yesitsfebreeze/feb42/pcb/feb42.kicad_sch

## KiCad design pcb/feb42.kicad_sch (2024-09-22)

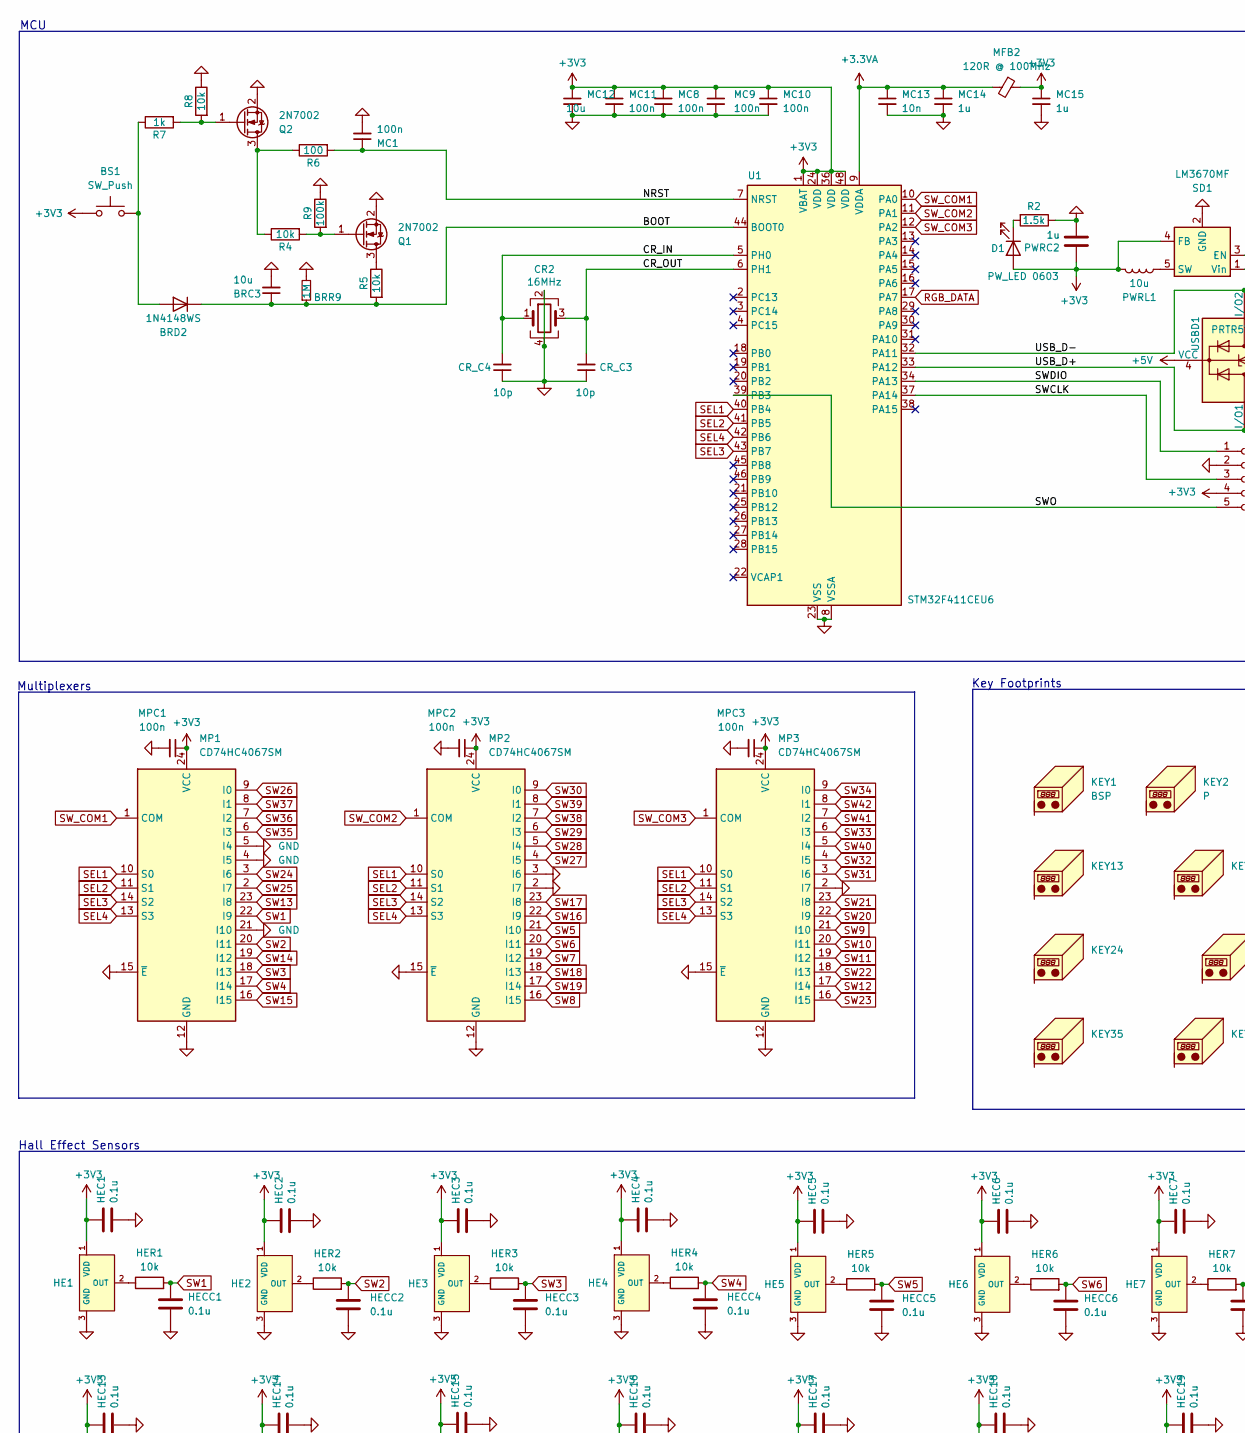
[picture p4: schematic feb42.kicad_sch, part in row 1, column 1]

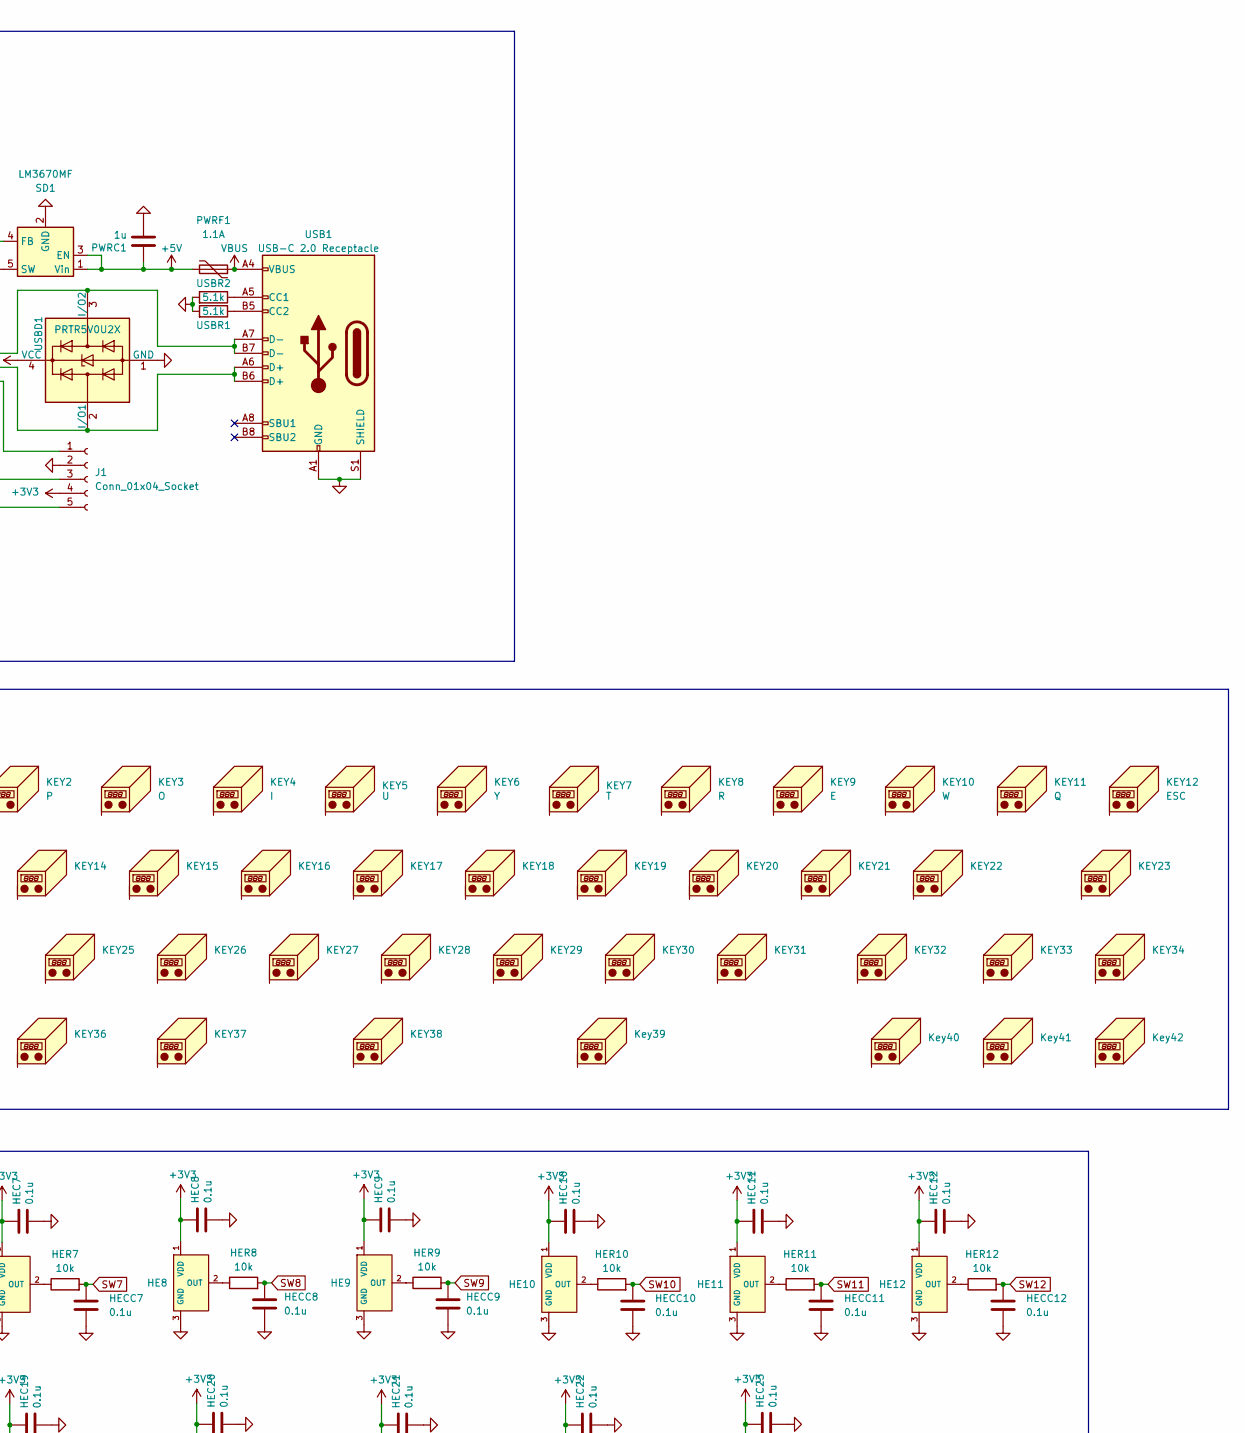
[picture p5: schematic feb42.kicad_sch, part in row 1, column 2]

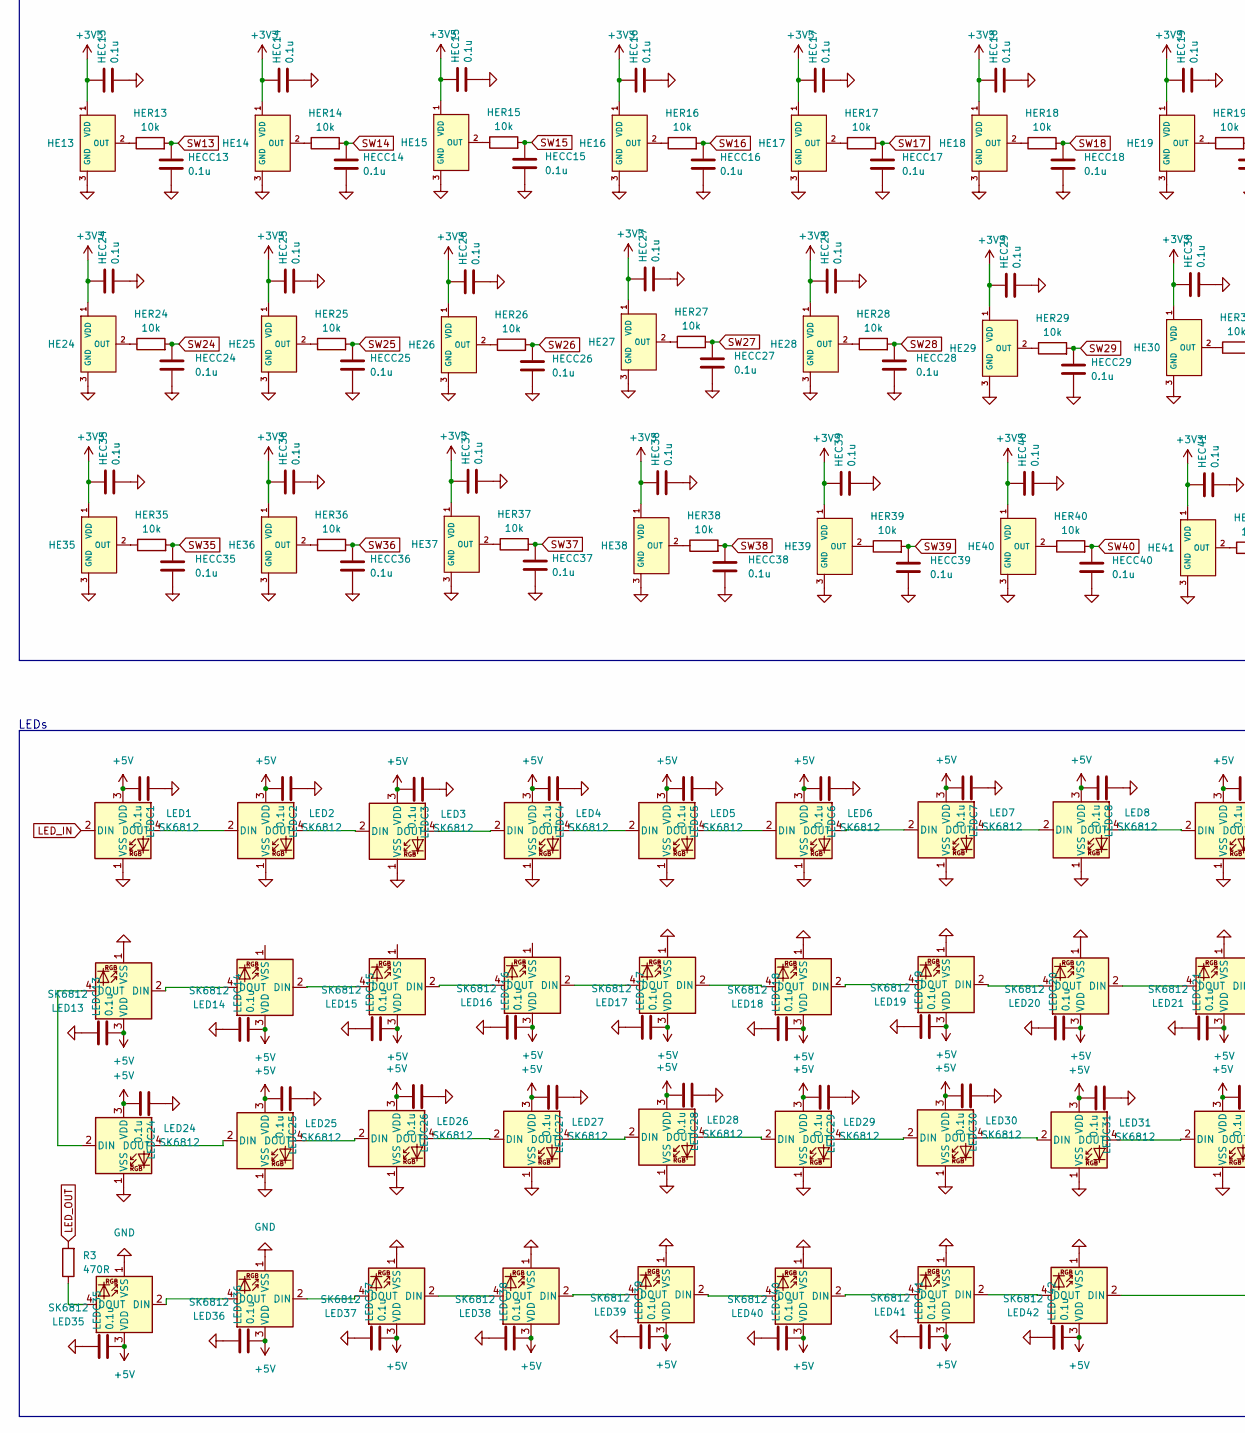
[picture p6: schematic feb42.kicad_sch, part in row 2, column 1]

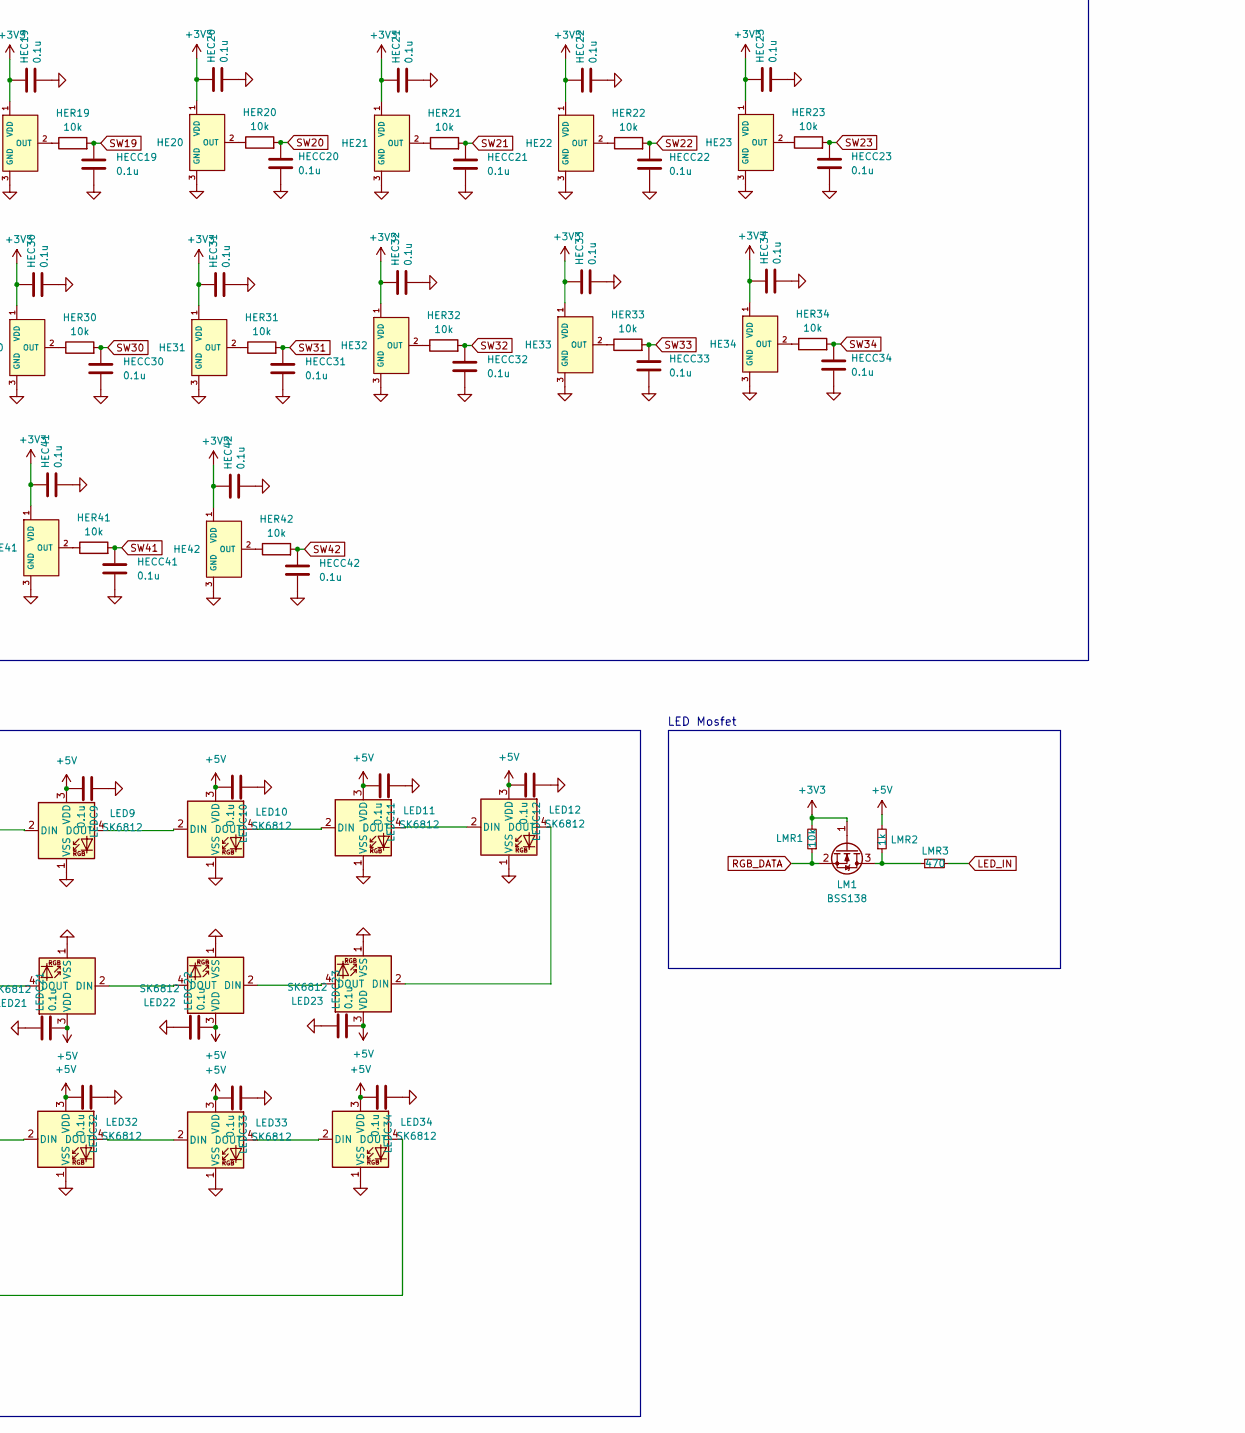
[picture p7: schematic feb42.kicad_sch, part in row 2, column 2]

Parts:
BRC3: 10u; C_1206_3216Metric; LCSC C13585
BRD2: 1N4148WS; D_SOD-323; LCSC C2128
BRR9: 1M; R_0402_1005Metric; LCSC C26083
BS1: SW_Push; SW_SPST_TL3342
CR2: 16MHz; Crystal_SMD_3225-4Pin_3.2x2.5mm; LCSC C13738
CR_C3, CR_C4: 10p; C_0402_1005Metric; LCSC C1525
D1: PW_LED 0603; LED_0603_1608Metric; LCSC C7371898
HE1, HE2, HE3, HE4, HE5, HE6, HE7, HE8, HE9, HE10, HE11, HE12, HE13, HE14, HE15, HE16, HE17, HE18, HE19, HE20, HE21, HE22, HE23, HE24, HE25, HE26, HE27, HE28, HE29, HE30, HE31, HE32, HE33, HE34, HE35, HE36, HE37, HE38, HE39, HE40, HE41, HE42: SLSS49E-3; SOT-23; LCSC C2904393
HEC1, HEC2, HEC3, HEC4, HEC5, HEC6, HEC7, HEC8, HEC9, HEC10, HEC11, HEC12, HEC13, HEC14, HEC15, HEC16, HEC17, HEC18, HEC19, HEC20, HEC21, HEC22, HEC23, HEC24, HEC25, HEC26, HEC27, HEC28, HEC29, HEC30, HEC31, HEC32, HEC33, HEC34, HEC35, HEC36, HEC37, HEC38, HEC39, HEC40, HEC41, HEC42: 0.1u; C_0402_1005Metric; LCSC C1525
HECC1, HECC2, HECC3, HECC4, HECC5, HECC6, HECC7, HECC8, HECC9, HECC10, HECC11, HECC12, HECC13, HECC14, HECC15, HECC16, HECC17, HECC18, HECC19, HECC20, HECC21, HECC22, HECC23, HECC24, HECC25, HECC26, HECC27, HECC28, HECC29, HECC30, HECC31, HECC32, HECC33, HECC34, HECC35, HECC36, HECC37, HECC38, HECC39, HECC40, HECC41, HECC42: 0.1u; C_0402_1005Metric; LCSC C1525
HER1, HER2, HER3, HER4, HER5, HER6, HER7, HER8, HER9, HER10, HER11, HER12, HER13, HER14, HER15, HER16, HER17, HER18, HER19, HER20, HER21, HER22, HER23, HER24, HER25, HER26, HER27, HER28, HER29, HER30, HER31, HER32, HER33, HER34, HER35, HER36, HER37, HER38, HER39, HER40, HER41, HER42: 10k; R_0402_1005Metric; LCSC C25744
J1: Conn_01x04_Socket; DBG_header
KEY1: BSP; HE_Switch_1.0U
KEY2: P; HE_Switch_1.0U
KEY3: O; HE_Switch_1.0U
KEY4: I; HE_Switch_1.0U
KEY5: U; HE_Switch_1.0U
KEY6: Y; HE_Switch_1.0U
KEY7: T; HE_Switch_1.0U
KEY8: R; HE_Switch_1.0U
KEY9: E; HE_Switch_1.0U
KEY10: W; HE_Switch_1.0U
KEY11: Q; HE_Switch_1.0U
KEY12: ESC; HE_Switch_1.0U
KEY13, KEY34: HE_Switch_1.75U
KEY14, KEY15, KEY16, KEY17, KEY18, KEY19, KEY20, KEY21, KEY22, KEY24, KEY25, KEY27, KEY28, KEY29, KEY30, KEY31, KEY33, KEY35, KEY36, KEY37: HE_Switch_1.0U
KEY23, KEY26, KEY32: HE_Switch_1.25U
KEY38: HE_Switch_2.75U
Key39: HE_Switch_2.25U
Key40, Key42: HE_Switch_1.25U
Key41: HE_Switch_1.0U
LED1, LED2, LED3, LED4, LED5, LED6, LED7, LED8, LED9, LED10, LED11, LED12, LED13, LED14, LED15, LED16, LED17, LED18, LED19, LED20, LED21, LED22, LED23, LED24, LED25, LED26, LED27, LED28, LED29, LED30, LED31, LED32, LED33, LED34, LED35, LED36, LED37, LED38, LED39, LED40, LED41, LED42: SK6812; SK6812-MINI-E; LCSC C5149201
LEDC1, LEDC2, LEDC3, LEDC4, LEDC5, LEDC6, LEDC7, LEDC8, LEDC9, LEDC10, LEDC11, LEDC12, LEDC13, LEDC14, LEDC15, LEDC16, LEDC17, LEDC18, LEDC19, LEDC20, LEDC21, LEDC22, LEDC23, LEDC24, LEDC25, LEDC26, LEDC27, LEDC28, LEDC29, LEDC30, LEDC31, LEDC32, LEDC33, LEDC34, LEDC35, LEDC36, LEDC37, LEDC38, LEDC39, LEDC40, LEDC41, LEDC42: 0.1u; C_0402_1005Metric
LM1: BSS138; SOT-23; LCSC C82045
LMR1: 10k; R_0402_1005Metric
LMR2: 1k; R_0402_1005Metric
LMR3: 470; R_0402_1005Metric
MC1, MC8, MC11: 100n; C_0402_1005Metric; MPN CL05B104KO5NNNC; LCSC C1525
MC9, MC10: 100n; C_0402_1005Metric; LCSC C1525
MC12: 10u; C_0402_1005Metric; MPN CL05B104KO5NNNC; LCSC C1525
MC13: 10n; C_0402_1005Metric; LCSC C307413
MC14, MC15: 1u; C_0402_1005Metric; LCSC C307413
MFB2: 120R @ 100MHz; L_0805_2012Metric; LCSC C1015
MP1, MP2, MP3: CD74HC4067SM; SSOP-24_5.3x8.2mm_P0.65mm; LCSC C98457
MPC1, MPC2, MPC3: 100n; C_0402_1005Metric; LCSC C1525
PWRC1, PWRC2: 1u; C_0805_2012Metric; LCSC Part C28323
PWRF1: 1.1A; Fuse_1206_3216Metric; LCSC C2760273
PWRL1: 10u; L_1210_3225Metric; LCSC C18184936
Q1, Q2: 2N7002; SOT-23; LCSC C8545
R2: 1.5k; R_0402_1005Metric; LCSC C25867
R3: 470R; R_0402_1005Metric
R4, R5, R8: 10k; R_0402_1005Metric; LCSC C25744
R6: 100; R_0402_1005Metric; LCSC C25076
R7: 1k; R_0402_1005Metric; LCSC C11702
R9: 100k; R_0402_1005Metric; LCSC C25741
SD1: LM3670MF; TSOT-23-5; LCSC C477918
U1: STM32F411CEU6; QFN-48-1EP_7x7mm_P0.5mm_EP5.6x5.6mm; LCSC C60420
USB1: USB-C 2.0 Receptacle; USB_C; LCSC C165948
USBD1: PRTR5V0U2X; SOT-143; LCSC C2827688
USBR1: 5.1k; R_0402_1005Metric; LCSC Part C25905
USBR2: 5.1k; R_0402_1005Metric; LCSC C25905

Connections:
+3.3VA: MC13.1, MC14.1, MFB2.2, U1.9 (VDDA)
+3V3: BS1.2, D1.2 (A), HE1.1 (VDD), HE2.1 (VDD), HE3.1 (VDD), HE4.1 (VDD), HE5.1 (VDD), HE6.1 (VDD), HE7.1 (VDD), HE8.1 (VDD), HE9.1 (VDD), HE10.1 (VDD), HE11.1 (VDD), HE12.1 (VDD), HE13.1 (VDD), HE14.1 (VDD), HE15.1 (VDD), HE16.1 (VDD), HE17.1 (VDD), HE18.1 (VDD), HE19.1 (VDD), HE20.1 (VDD), HE21.1 (VDD), HE22.1 (VDD), HE23.1 (VDD), HE24.1 (VDD), HE25.1 (VDD), HE26.1 (VDD), HE27.1 (VDD), HE28.1 (VDD), HE29.1 (VDD), HE30.1 (VDD), HE31.1 (VDD), HE32.1 (VDD), HE33.1 (VDD), HE34.1 (VDD), HE35.1 (VDD), HE36.1 (VDD), HE37.1 (VDD), HE38.1 (VDD), HE39.1 (VDD), HE40.1 (VDD), HE41.1 (VDD), HE42.1 (VDD), HEC1.1, HEC2.1, HEC3.1, HEC4.1, HEC5.1, HEC6.1, HEC7.1, HEC8.1, HEC9.1, HEC10.1, HEC11.1, HEC12.1, HEC13.1, HEC14.1, HEC15.1, HEC16.1, HEC17.1, HEC18.1, HEC19.1, HEC20.1, HEC21.1, HEC22.1, HEC23.1, HEC24.1, HEC25.1, HEC26.1, HEC27.1, HEC28.1, HEC29.1, HEC30.1, HEC31.1, HEC32.1, HEC33.1, HEC34.1, HEC35.1, HEC36.1, HEC37.1, HEC38.1, HEC39.1, HEC40.1, HEC41.1, HEC42.1, J1.4, LM1.1 (G), LMR1.2, MC8.1, MC9.1, MC10.1, MC11.1, MC12.1, MC15.1, MFB2.1, MP1.24 (VCC), MP2.24 (VCC), MP3.24 (VCC), MPC1.1, MPC2.1, MPC3.1, PWRC2.1, PWRL1.1, SD1.4 (FB), U1.1 (VBAT), U1.24 (VDD), U1.36 (VDD), U1.48 (VDD)
+5V: LED1.3 (VDD), LED2.3 (VDD), LED3.3 (VDD), LED4.3 (VDD), LED5.3 (VDD), LED6.3 (VDD), LED7.3 (VDD), LED8.3 (VDD), LED9.3 (VDD), LED10.3 (VDD), LED11.3 (VDD), LED12.3 (VDD), LED13.3 (VDD), LED14.3 (VDD), LED15.3 (VDD), LED16.3 (VDD), LED17.3 (VDD), LED18.3 (VDD), LED19.3 (VDD), LED20.3 (VDD), LED21.3 (VDD), LED22.3 (VDD), LED23.3 (VDD), LED24.3 (VDD), LED25.3 (VDD), LED26.3 (VDD), LED27.3 (VDD), LED28.3 (VDD), LED29.3 (VDD), LED30.3 (VDD), LED31.3 (VDD), LED32.3 (VDD), LED33.3 (VDD), LED34.3 (VDD), LED35.3 (VDD), LED36.3 (VDD), LED37.3 (VDD), LED38.3 (VDD), LED39.3 (VDD), LED40.3 (VDD), LED41.3 (VDD), LED42.3 (VDD), LEDC1.2, LEDC2.2, LEDC3.2, LEDC4.2, LEDC5.2, LEDC6.2, LEDC7.2, LEDC8.2, LEDC9.2, LEDC10.2, LEDC11.2, LEDC12.2, LEDC13.2, LEDC14.2, LEDC15.2, LEDC16.2, LEDC17.2, LEDC18.2, LEDC19.2, LEDC20.2, LEDC21.2, LEDC22.2, LEDC23.2, LEDC24.2, LEDC25.2, LEDC26.2, LEDC27.2, LEDC28.2, LEDC29.2, LEDC30.2, LEDC31.2, LEDC32.2, LEDC33.2, LEDC34.2, LEDC35.2, LEDC36.2, LEDC37.2, LEDC38.2, LEDC39.2, LEDC40.2, LEDC41.2, LEDC42.2, LMR2.2, PWRC1.1, PWRF1.2, SD1.1 (Vin), SD1.3 (EN), USBD1.4 (VCC)
BOOT: BRC3.1, BRD2.1 (K), BRR9.1, R5.2, U1.44 (BOOT0)
CR_IN: CR2.1, CR_C4.2, U1.5 (PH0)
CR_OUT: CR2.3, CR_C3.2, U1.6 (PH1)
GND: BRC3.2, BRR9.2, CR2.2, CR2.4, CR_C3.1, CR_C4.1, HE1.3 (GND), HE2.3 (GND), HE3.3 (GND), HE4.3 (GND), HE5.3 (GND), HE6.3 (GND), HE7.3 (GND), HE8.3 (GND), HE9.3 (GND), HE10.3 (GND), HE11.3 (GND), HE12.3 (GND), HE13.3 (GND), HE14.3 (GND), HE15.3 (GND), HE16.3 (GND), HE17.3 (GND), HE18.3 (GND), HE19.3 (GND), HE20.3 (GND), HE21.3 (GND), HE22.3 (GND), HE23.3 (GND), HE24.3 (GND), HE25.3 (GND), HE26.3 (GND), HE27.3 (GND), HE28.3 (GND), HE29.3 (GND), HE30.3 (GND), HE31.3 (GND), HE32.3 (GND), HE33.3 (GND), HE34.3 (GND), HE35.3 (GND), HE36.3 (GND), HE37.3 (GND), HE38.3 (GND), HE39.3 (GND), HE40.3 (GND), HE41.3 (GND), HE42.3 (GND), HEC1.2, HEC2.2, HEC3.2, HEC4.2, HEC5.2, HEC6.2, HEC7.2, HEC8.2, HEC9.2, HEC10.2, HEC11.2, HEC12.2, HEC13.2, HEC14.2, HEC15.2, HEC16.2, HEC17.2, HEC18.2, HEC19.2, HEC20.2, HEC21.2, HEC22.2, HEC23.2, HEC24.2, HEC25.2, HEC26.2, HEC27.2, HEC28.2, HEC29.2, HEC30.2, HEC31.2, HEC32.2, HEC33.2, HEC34.2, HEC35.2, HEC36.2, HEC37.2, HEC38.2, HEC39.2, HEC40.2, HEC41.2, HEC42.2, HECC1.2, HECC2.2, HECC3.2, HECC4.2, HECC5.2, HECC6.2, HECC7.2, HECC8.2, HECC9.2, HECC10.2, HECC11.2, HECC12.2, HECC13.2, HECC14.2, HECC15.2, HECC16.2, HECC17.2, HECC18.2, HECC19.2, HECC20.2, HECC21.2, HECC22.2, HECC23.2, HECC24.2, HECC25.2, HECC26.2, HECC27.2, HECC28.2, HECC29.2, HECC30.2, HECC31.2, HECC32.2, HECC33.2, HECC34.2, HECC35.2, HECC36.2, HECC37.2, HECC38.2, HECC39.2, HECC40.2, HECC41.2, HECC42.2, J1.2, LED1.1 (VSS), LED2.1 (VSS), LED3.1 (VSS), LED4.1 (VSS), LED5.1 (VSS), LED6.1 (VSS), LED7.1 (VSS), LED8.1 (VSS), LED9.1 (VSS), LED10.1 (VSS), LED11.1 (VSS), LED12.1 (VSS), LED13.1 (VSS), LED17.1 (VSS), LED18.1 (VSS), LED19.1 (VSS), LED20.1 (VSS), LED21.1 (VSS), LED22.1 (VSS), LED23.1 (VSS), LED24.1 (VSS), LED25.1 (VSS), LED26.1 (VSS), LED27.1 (VSS), LED28.1 (VSS), LED29.1 (VSS), LED30.1 (VSS), LED31.1 (VSS), LED32.1 (VSS), LED33.1 (VSS), LED34.1 (VSS), LED35.1 (VSS), LED36.1 (VSS), LED37.1 (VSS), LED38.1 (VSS), LED39.1 (VSS), LED40.1 (VSS), LED41.1 (VSS), LED42.1 (VSS), LEDC1.1, LEDC2.1, LEDC3.1, LEDC4.1, LEDC5.1, LEDC6.1, LEDC7.1, LEDC8.1, LEDC9.1, LEDC10.1, LEDC11.1, LEDC12.1, LEDC13.1, LEDC14.1, LEDC15.1, LEDC16.1, LEDC17.1, LEDC18.1, LEDC19.1, LEDC20.1, LEDC21.1, LEDC22.1, LEDC23.1, LEDC24.1, LEDC25.1, LEDC26.1, LEDC27.1, LEDC28.1, LEDC29.1, LEDC30.1, LEDC31.1, LEDC32.1, LEDC33.1, LEDC34.1, LEDC35.1, LEDC36.1, LEDC37.1, LEDC38.1, LEDC39.1, LEDC40.1, LEDC41.1, LEDC42.1, MC1.2, MC8.2, MC9.2, MC10.2, MC11.2, MC12.2, MC13.2, MC14.2, MC15.2, MP1.4 (I5), MP1.5 (I4), MP1.12 (GND), MP1.15 (~E), MP1.21 (I10), MP2.2 (I7), MP2.3 (I6), MP2.12 (GND), MP2.15 (~E), MP3.2 (I7), MP3.12 (GND), MP3.15 (~E), MPC1.2, MPC2.2, MPC3.2, PWRC1.2, PWRC2.2, Q1.2 (S), Q2.2 (S), R2.1, R8.1, R9.1, SD1.2 (GND), U1.8 (VSSA), U1.23 (VSS), U1.35 (VSS), U1.47 (VSS), U1.49 (VSS), USB1.A1 (GND), USB1.A12 (GND), USB1.B1 (GND), USB1.B12 (GND), USB1.S1 (SHIELD), USBD1.1 (GND), USBR1.2, USBR2.2
LED_IN: LED1.2 (DIN), LMR3.2
LED_OUT: R3.2
NRST: MC1.1, R6.2, U1.7 (NRST)
unnamed: BRD2.2 (A), BS1.1, R7.1
unnamed: D1.1 (K), R2.2
unnamed: HE1.2 (OUT), HER1.1
unnamed: HE2.2 (OUT), HER2.1
unnamed: HE3.2 (OUT), HER3.1
unnamed: HE4.2 (OUT), HER4.1
unnamed: HE5.2 (OUT), HER5.1
unnamed: HE6.2 (OUT), HER6.1
unnamed: HE7.2 (OUT), HER7.1
unnamed: HE8.2 (OUT), HER8.1
unnamed: HE9.2 (OUT), HER9.1
unnamed: HE10.2 (OUT), HER10.1
unnamed: HE11.2 (OUT), HER11.1
unnamed: HE12.2 (OUT), HER12.1
unnamed: HE13.2 (OUT), HER13.1
unnamed: HE14.2 (OUT), HER14.1
unnamed: HE15.2 (OUT), HER15.1
unnamed: HE16.2 (OUT), HER16.1
unnamed: HE17.2 (OUT), HER17.1
unnamed: HE18.2 (OUT), HER18.1
unnamed: HE19.2 (OUT), HER19.1
unnamed: HE20.2 (OUT), HER20.1
unnamed: HE21.2 (OUT), HER21.1
unnamed: HE22.2 (OUT), HER22.1
unnamed: HE23.2 (OUT), HER23.1
unnamed: HE24.2 (OUT), HER24.1
unnamed: HE25.2 (OUT), HER25.1
unnamed: HE26.2 (OUT), HER26.1
unnamed: HE27.2 (OUT), HER27.1
unnamed: HE28.2 (OUT), HER28.1
unnamed: HE29.2 (OUT), HER29.1
unnamed: HE30.2 (OUT), HER30.1
unnamed: HE31.2 (OUT), HER31.1
unnamed: HE32.2 (OUT), HER32.1
unnamed: HE33.2 (OUT), HER33.1
unnamed: HE34.2 (OUT), HER34.1
unnamed: HE35.2 (OUT), HER35.1
unnamed: HE36.2 (OUT), HER36.1
unnamed: HE37.2 (OUT), HER37.1
unnamed: HE38.2 (OUT), HER38.1
unnamed: HE39.2 (OUT), HER39.1
unnamed: HE40.2 (OUT), HER40.1
unnamed: HE41.2 (OUT), HER41.1
unnamed: HE42.2 (OUT), HER42.1
unnamed: LED1.4 (DOUT), LED2.2 (DIN)
unnamed: LED2.4 (DOUT), LED3.2 (DIN)
unnamed: LED3.4 (DOUT), LED4.2 (DIN)
unnamed: LED4.4 (DOUT), LED5.2 (DIN)
unnamed: LED5.4 (DOUT), LED6.2 (DIN)
unnamed: LED6.4 (DOUT), LED7.2 (DIN)
unnamed: LED7.4 (DOUT), LED8.2 (DIN)
unnamed: LED8.4 (DOUT), LED9.2 (DIN)
unnamed: LED9.4 (DOUT), LED10.2 (DIN)
unnamed: LED10.4 (DOUT), LED11.2 (DIN)
unnamed: LED11.4 (DOUT), LED12.2 (DIN)
unnamed: LED12.4 (DOUT), LED23.2 (DIN)
unnamed: LED13.2 (DIN), LED14.4 (DOUT)
unnamed: LED13.4 (DOUT), LED24.2 (DIN)
unnamed: LED14.2 (DIN), LED15.4 (DOUT)
unnamed: LED15.2 (DIN), LED16.4 (DOUT)
unnamed: LED16.2 (DIN), LED17.4 (DOUT)
unnamed: LED17.2 (DIN), LED18.4 (DOUT)
unnamed: LED18.2 (DIN), LED19.4 (DOUT)
unnamed: LED19.2 (DIN), LED20.4 (DOUT)
unnamed: LED20.2 (DIN), LED21.4 (DOUT)
unnamed: LED21.2 (DIN), LED22.4 (DOUT)
unnamed: LED22.2 (DIN), LED23.4 (DOUT)
unnamed: LED24.4 (DOUT), LED25.2 (DIN)
unnamed: LED25.4 (DOUT), LED26.2 (DIN)
unnamed: LED26.4 (DOUT), LED27.2 (DIN)
unnamed: LED27.4 (DOUT), LED28.2 (DIN)
unnamed: LED28.4 (DOUT), LED29.2 (DIN)
unnamed: LED29.4 (DOUT), LED30.2 (DIN)
unnamed: LED30.4 (DOUT), LED31.2 (DIN)
unnamed: LED31.4 (DOUT), LED32.2 (DIN)
unnamed: LED32.4 (DOUT), LED33.2 (DIN)
unnamed: LED33.4 (DOUT), LED34.2 (DIN)
unnamed: LED34.4 (DOUT), LED42.2 (DIN)
unnamed: LED35.2 (DIN), LED36.4 (DOUT)
unnamed: LED35.4 (DOUT), R3.1
unnamed: LED36.2 (DIN), LED37.4 (DOUT)
unnamed: LED37.2 (DIN), LED38.4 (DOUT)
unnamed: LED38.2 (DIN), LED39.4 (DOUT)
unnamed: LED39.2 (DIN), LED40.4 (DOUT)
unnamed: LED40.2 (DIN), LED41.4 (DOUT)
unnamed: LED41.2 (DIN), LED42.4 (DOUT)
unnamed: LM1.3 (D), LMR2.1, LMR3.1
unnamed: PWRL1.2, SD1.5 (SW)
unnamed: Q1.1 (G), R4.2, R9.2
unnamed: Q1.3 (D), R5.1
unnamed: Q2.1 (G), R7.2, R8.2
unnamed: Q2.3 (D), R4.1, R6.1
unnamed: USB1.A5 (CC1), USBR2.1
unnamed: USB1.B5 (CC2), USBR1.1
RGB_DATA: LM1.2 (S), LMR1.1, U1.17 (PA7)
SEL1: MP1.10 (S0), MP2.10 (S0), MP3.10 (S0), U1.40 (PB4)
SEL2: MP1.11 (S1), MP2.11 (S1), MP3.11 (S1), U1.41 (PB5)
SEL3: MP1.14 (S2), MP2.14 (S2), MP3.14 (S2), U1.43 (PB7)
SEL4: MP1.13 (S3), MP2.13 (S3), MP3.13 (S3), U1.42 (PB6)
SW1: HECC1.1, HER1.2, MP1.22 (I9)
SW2: HECC2.1, HER2.2, MP1.20 (I11)
SW3: HECC3.1, HER3.2, MP1.18 (I13)
SW4: HECC4.1, HER4.2, MP1.17 (I14)
SW5: HECC5.1, HER5.2, MP2.21 (I10)
SW6: HECC6.1, HER6.2, MP2.20 (I11)
SW7: HECC7.1, HER7.2, MP2.19 (I12)
SW8: HECC8.1, HER8.2, MP2.16 (I15)
SW9: HECC9.1, HER9.2, MP3.21 (I10)
SW10: HECC10.1, HER10.2, MP3.20 (I11)
SW11: HECC11.1, HER11.2, MP3.19 (I12)
SW12: HECC12.1, HER12.2, MP3.17 (I14)
SW13: HECC13.1, HER13.2, MP1.23 (I8)
SW14: HECC14.1, HER14.2, MP1.19 (I12)
SW15: HECC15.1, HER15.2, MP1.16 (I15)
SW16: HECC16.1, HER16.2, MP2.22 (I9)
SW17: HECC17.1, HER17.2, MP2.23 (I8)
SW18: HECC18.1, HER18.2, MP2.18 (I13)
SW19: HECC19.1, HER19.2, MP2.17 (I14)
SW20: HECC20.1, HER20.2, MP3.22 (I9)
SW21: HECC21.1, HER21.2, MP3.23 (I8)
SW22: HECC22.1, HER22.2, MP3.18 (I13)
SW23: HECC23.1, HER23.2, MP3.16 (I15)
SW24: HECC24.1, HER24.2, MP1.3 (I6)
SW25: HECC25.1, HER25.2, MP1.2 (I7)
SW26: HECC26.1, HER26.2, MP1.9 (I0)
SW27: HECC27.1, HER27.2, MP2.4 (I5)
SW28: HECC28.1, HER28.2, MP2.5 (I4)
SW29: HECC29.1, HER29.2, MP2.6 (I3)
SW30: HECC30.1, HER30.2, MP2.9 (I0)
SW31: HECC31.1, HER31.2, MP3.3 (I6)
SW32: HECC32.1, HER32.2, MP3.4 (I5)
SW33: HECC33.1, HER33.2, MP3.6 (I3)
SW34: HECC34.1, HER34.2, MP3.9 (I0)
SW35: HECC35.1, HER35.2, MP1.6 (I3)
SW36: HECC36.1, HER36.2, MP1.7 (I2)
SW37: HECC37.1, HER37.2, MP1.8 (I1)
SW38: HECC38.1, HER38.2, MP2.7 (I2)
SW39: HECC39.1, HER39.2, MP2.8 (I1)
SW40: HECC40.1, HER40.2, MP3.5 (I4)
SW41: HECC41.1, HER41.2, MP3.7 (I2)
SW42: HECC42.1, HER42.2, MP3.8 (I1)
SWCLK: J1.3, U1.37 (PA14)
SWDIO: J1.1, U1.34 (PA13)
SWO: J1.5, U1.39 (PB3)
SW_COM1: MP1.1 (COM), U1.10 (PA0)
SW_COM2: MP2.1 (COM), U1.11 (PA1)
SW_COM3: MP3.1 (COM), U1.12 (PA2)
USB_D+: U1.33 (PA12), USB1.A6 (D+), USB1.B6 (D+), USBD1.2 (I/O1)
USB_D-: U1.32 (PA11), USB1.A7 (D-), USB1.B7 (D-), USBD1.3 (I/O2)
VBUS: PWRF1.1, USB1.A4 (VBUS), USB1.A9 (VBUS), USB1.B4 (VBUS), USB1.B9 (VBUS)

Notes on the sheet:
Multiplexers
LEDs
Key Footprints
Hall Effect Sensors
MCU
LED Mosfet
